AKAMEDIASYSTEM/LEVER/LEVER-firmware-enc/waves.ino

// not used right now
//
//const int sineW[512] = {2048,2073,2098,2123,2148,2173,2198,2223,
//2248,2273,2298,2323,2348,2373,2398,2422,
//2447,2472,2496,2521,2545,2569,2594,2618,
//2642,2666,2690,2714,2737,2761,2784,2808,
//2831,2854,2877,2900,2923,2946,2968,2990,
//3013,3035,3057,3078,3100,3122,3143,3164,
//3185,3206,3226,3247,3267,3287,3307,3327,
//3346,3366,3385,3404,3423,3441,3459,3477,
//3495,3513,3530,3548,3565,3581,3598,3614,
//3630,3646,3662,3677,3692,3707,3722,3736,
//3750,3764,3777,3791,3804,3816,3829,3841,
//3853,3865,3876,3888,3898,3909,3919,3929,
//3939,3949,3958,3967,3975,3984,3992,3999,
//4007,4014,4021,4027,4034,4040,4045,4051,
//4056,4060,4065,4069,4073,4076,4080,4083,
//4085,4087,4089,4091,4093,4094,4094,4095,
//4095,4095,4094,4094,4093,4091,4089,4087,
//4085,4083,4080,4076,4073,4069,4065,4060,
//4056,4051,4045,4040,4034,4027,4021,4014,
//4007,3999,3992,3984,3975,3967,3958,3949,
//3939,3929,3919,3909,3898,3888,3876,3865,
//3853,3841,3829,3816,3804,3791,3777,3764,
//3750,3736,3722,3707,3692,3677,3662,3646,
//3630,3614,3598,3581,3565,3548,3530,3513,
//3495,3477,3459,3441,3423,3404,3385,3366,
//3346,3327,3307,3287,3267,3247,3226,3206,
//3185,3164,3143,3122,3100,3078,3057,3035,
//3013,2990,2968,2946,2923,2900,2877,2854,
//2831,2808,2784,2761,2737,2714,2690,2666,
//2642,2618,2594,2569,2545,2521,2496,2472,
//2447,2422,2398,2373,2348,2323,2298,2273,
//2248,2223,2198,2173,2148,2123,2098,2073,
//2048,2022,1997,1972,1947,1922,1897,1872,
//1847,1822,1797,1772,1747,1722,1697,1673,
//1648,1623,1599,1574,1550,1526,1501,1477,
//1453,1429,1405,1381,1358,1334,1311,1287,
//1264,1241,1218,1195,1172,1149,1127,1105,
//1082,1060,1038,1017,995,973,952,931,
//910,889,869,848,828,808,788,768,
//749,729,710,691,672,654,636,618,
//600,582,565,547,530,514,497,481,
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
